Corinyi/Auto_Balancing_Bike/stl file/rear tire.stl

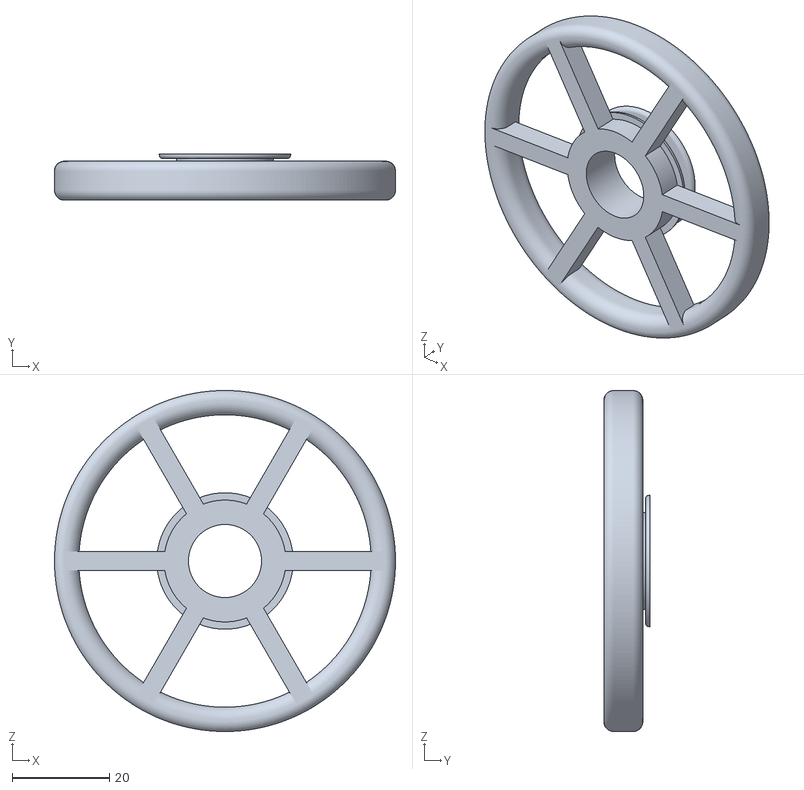
[picture p22: CAD file, 2020-03-20]
stl file/rear tire.stl
70.0 x 9.50 x 70.0
