Corinyi/Auto_Balancing_Bike/stl file/handle gear.stl

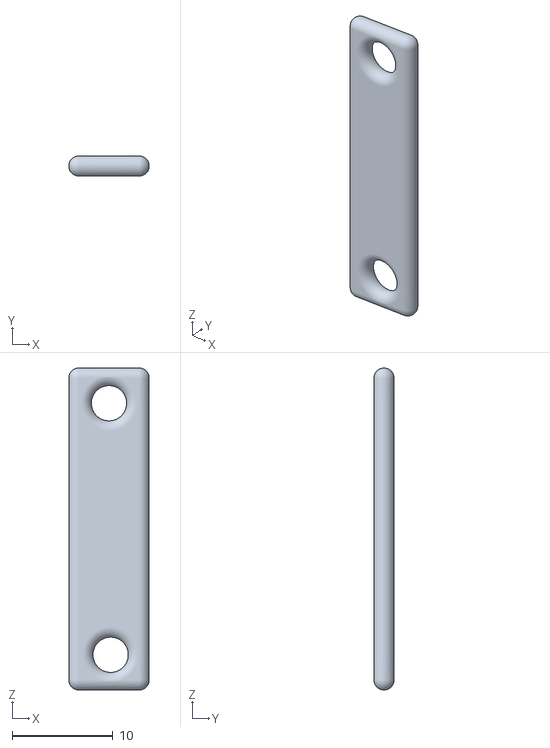
[picture p23: CAD file, 2020-03-20]
stl file/handle gear.stl
8.00 x 2.00 x 32.0
