Corinyi/Auto_Balancing_Bike/stl file/bal.stl

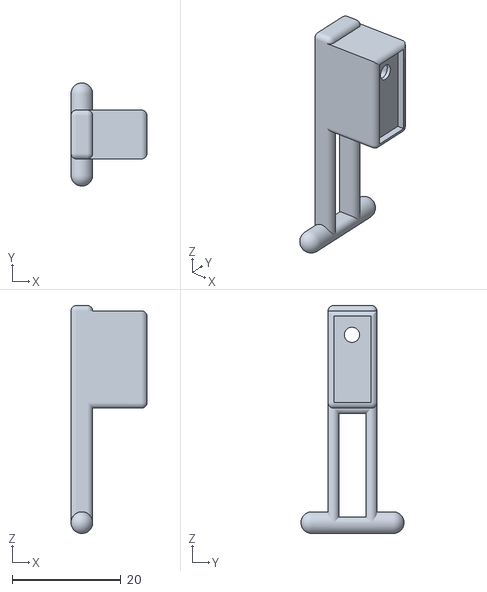
[picture p24: CAD file, 2020-03-20]
stl file/bal.stl
14.0 x 19.0 x 42.0
