Corinyi/Auto_Balancing_Bike/stl file/gojung.stl

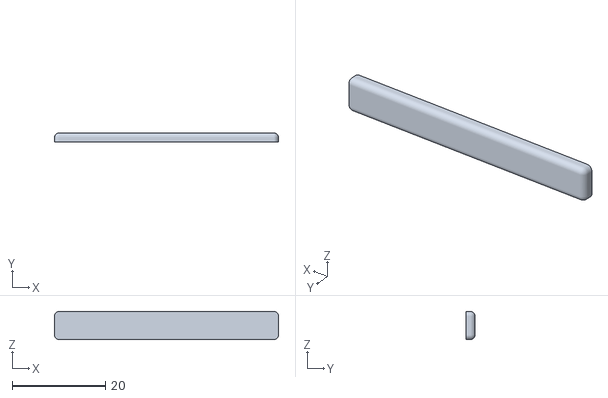
[picture p25: CAD file, 2020-03-20]
stl file/gojung.stl
48.0 x 2.00 x 6.00
