Corinyi/Auto_Balancing_Bike/stl file/front tire.stl

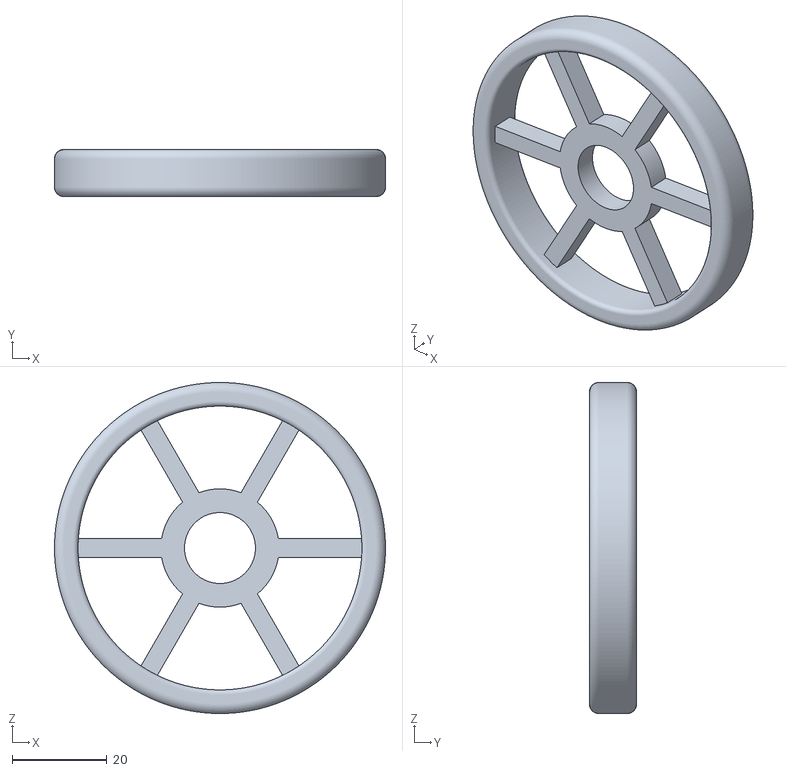
[picture p26: CAD file, 2020-03-20]
stl file/front tire.stl
70.0 x 10.0 x 70.0
